sapperxl/Dual-Speaker-Mic-Voice-Assistant/Voice Assistant.kicad_sch

## KiCad design Voice Assistant.kicad_sch (2026-05-18)

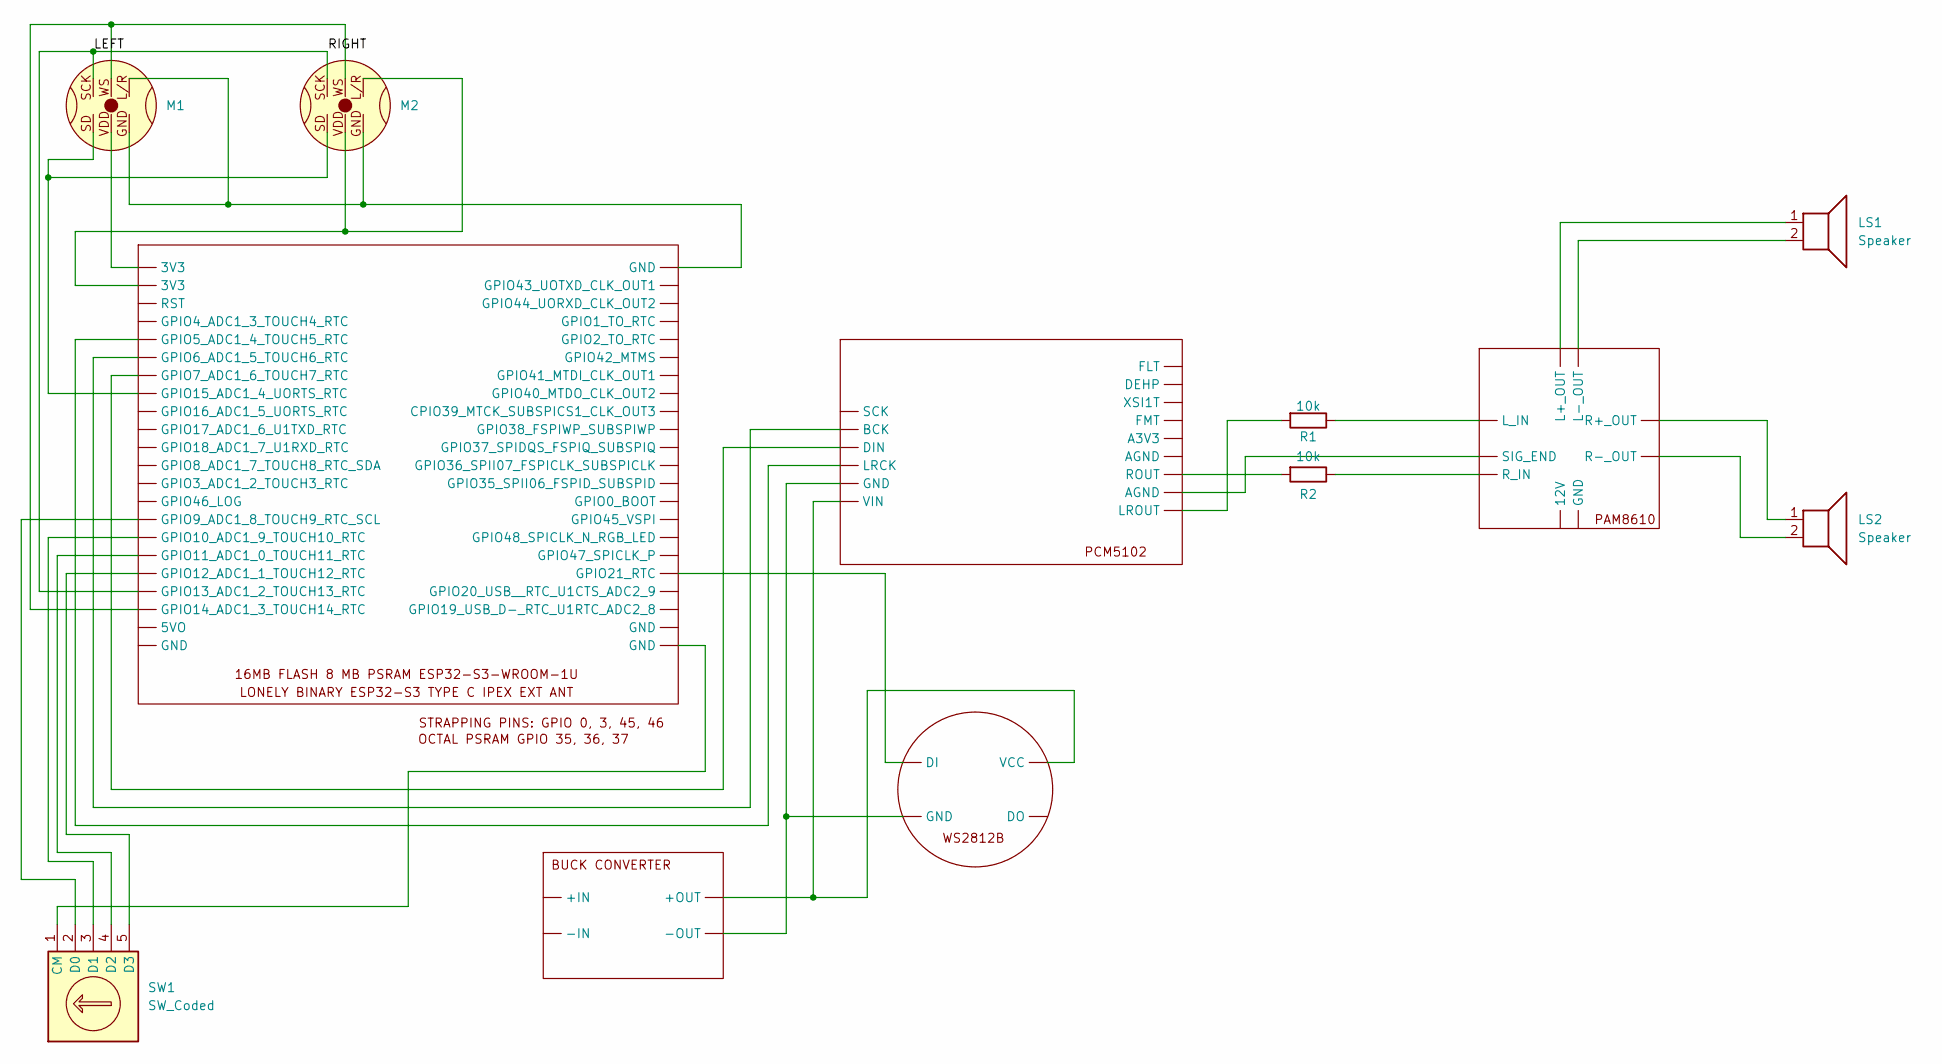
[picture p10: schematic Voice Assistant.kicad_sch]

Parts:
GENERIC BUCK CONV1: (no value)
LS1, LS2: Speaker
M1, M2: (no value)
PAM8610 Module2: (no value)
R1, R2: 10k
SW1: SW_Coded
U1, U2, U3: (no value)

Connections:
LEFT: M1.SCK, M2.SCK, U1.
unnamed: GENERIC BUCK CONV1., U2., U3.
unnamed: LS1.1, PAM8610 Module2.
unnamed: LS1.2, PAM8610 Module2.
unnamed: LS2.1, PAM8610 Module2.
unnamed: LS2.2, PAM8610 Module2.
unnamed: M1.GND, M1.L/R, M2.GND, U1.
unnamed: M1.SD, M2.SD, U1.
unnamed: M1.VDD, U1.
unnamed: M1.WS, M2.WS, U1.
unnamed: M2.L/R, M2.VDD, U1.
unnamed: PAM8610 Module2., R1.1, R2.1, U2.
unnamed: R1.2, U2.
unnamed: R2.2, U2.
unnamed: SW1.1 (CM), U1.
unnamed: SW1.2 (D0), U1.
unnamed: SW1.3 (D1), U1.
unnamed: SW1.4 (D2), U1.
unnamed: SW1.5 (D3), U1.
unnamed: U1., U2., U3.
